PeterJensen/swim-cam/www/00000000-0.jpg

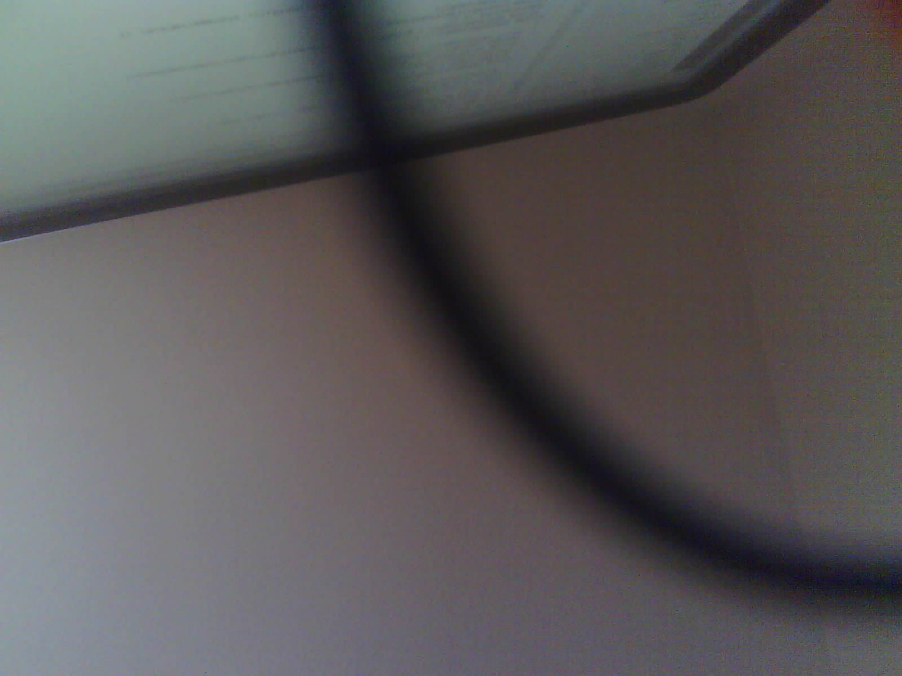
www/00000000-0.jpg
