PeterJensen/swim-cam/www/00000000-2.jpg

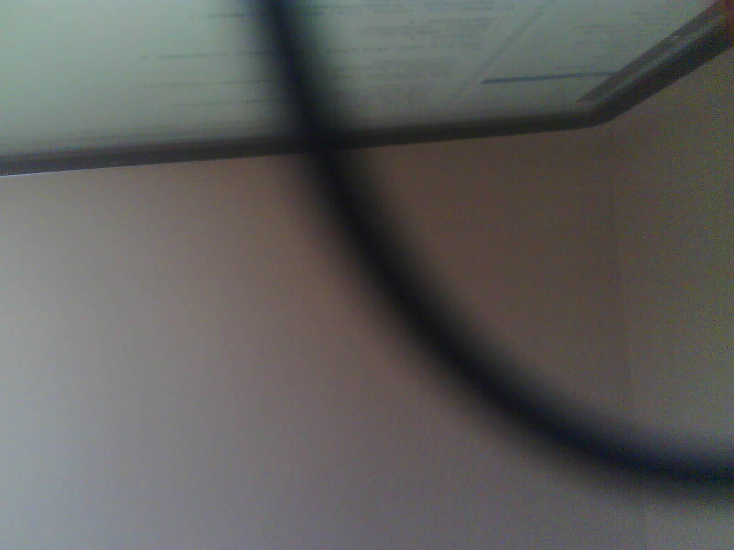
www/00000000-2.jpg
