PeterJensen/swim-cam/www/00000000-3.jpg

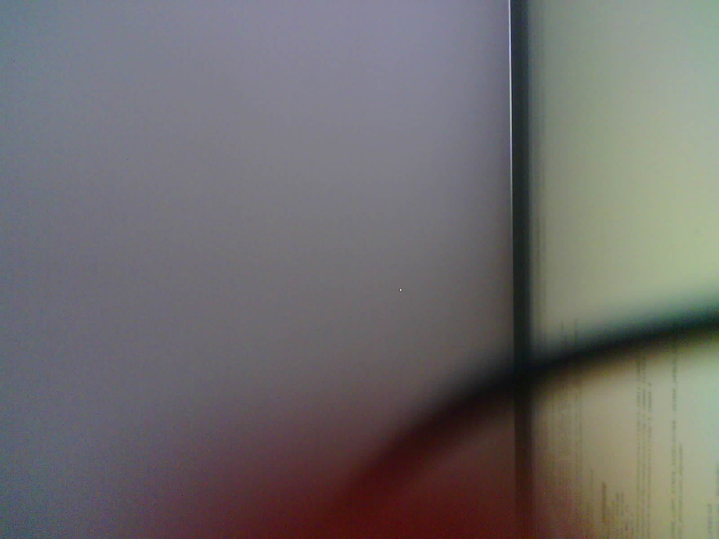
www/00000000-3.jpg
